muonTelescope/mppcSensor/pcb/mppcSensor.kicad_sch

## KiCad design pcb/mppcSensor.kicad_sch (2022-10-26)

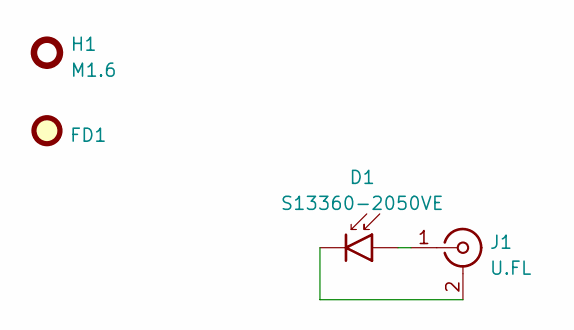
[picture p10: schematic mppcSensor.kicad_sch]

Parts:
D1: S13360-2050VE
FD1: Fiducial; Fiducial_1.5mm_Mask3mm
H1: M1.6
J1: U.FL

Connections:
unnamed: D1.A, J1.1 (In)
unnamed: D1.K, J1.2 (Ext)
